biobotproject-org/biobot-hardware/pcb/pluh/pluh.kicad_sch

## KiCad design pcb/pluh/pluh.kicad_sch (2026-04-02)

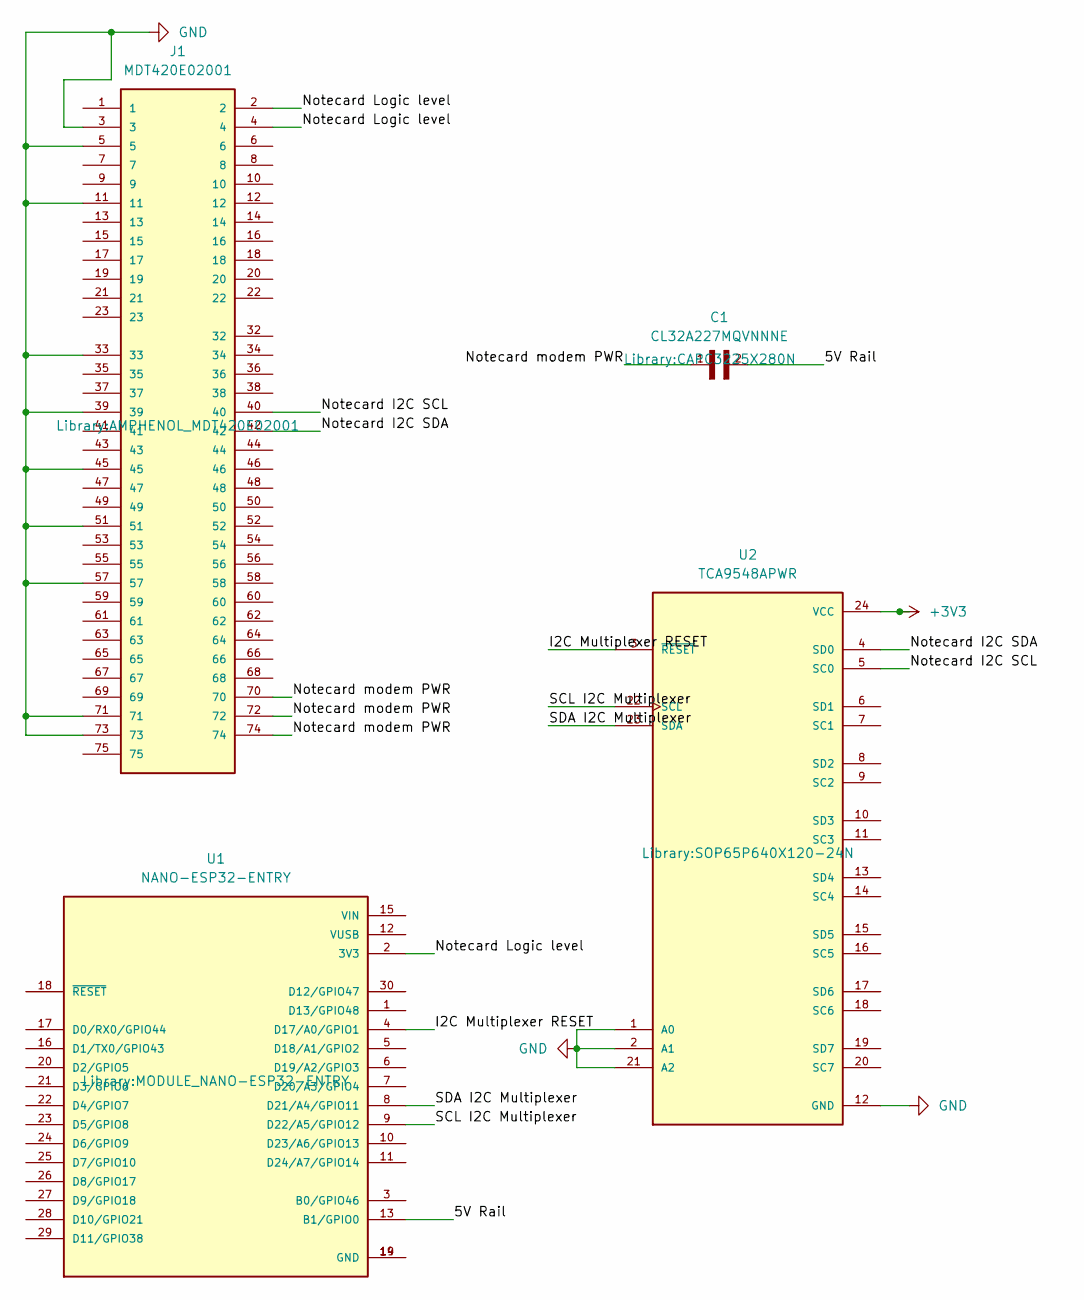
[picture p9: schematic pluh.kicad_sch]

Parts:
C1: CL32A227MQVNNNE; CAPC3225X280N; DigiKey_Part_Number 1276-3375-1-ND
J1: MDT420E02001; AMPHENOL_MDT420E02001; PARTREV 7; DigiKey_Part_Number MDT420E02001-ND
U1: NANO-ESP32-ENTRY; MODULE_NANO-ESP32-ENTRY; PARTREV 08/07/2025
U2: TCA9548APWR; SOP65P640X120-24N; PARTREV G

Connections:
5V Rail: C1.2, U1.13 (B1/GPIO0)
+3V3: U2.24 (VCC)
GND: J1.3, J1.5, J1.11, J1.33, J1.39, J1.45, J1.51, J1.57, J1.71, J1.73, U2.1 (A0), U2.2 (A1), U2.12 (GND), U2.21 (A2)
I2C Multiplexer RESET: U1.4 (D17/A0/GPIO1), U2.3 (~RESET)
unnamed: U1.14 (GND), U1.19 (GND)
Notecard I2C SCL: J1.40, U2.5 (SC0)
Notecard I2C SDA: J1.42, U2.4 (SD0)
Notecard Logic level: J1.2, J1.4, U1.2 (3V3)
Notecard modem PWR: C1.1, J1.70, J1.72, J1.74
SCL I2C Multiplexer: U1.9 (D22/A5/GPIO12), U2.22 (SCL)
SDA I2C Multiplexer: U1.8 (D21/A4/GPIO11), U2.23 (SDA)
